cSDes1gn/ucl/src/logger.c

#include "logger.h"
#include "usart.h"
#include <stdarg.h>

// program log level (disable by default)
static enum log_level _level = LOG_DISABLE;

/**
 * @brief Get the string representation of log level enum
 *
 * @param level log level enum
 * @return char*
 */
static char *_get_level_str(enum log_level level) {
  switch (level) {
    case LOG_TRACE:
      return "TRACE";
    case LOG_INFO:
      return "INFO";
    case LOG_WARNING:
      return "WARN";
    case LOG_ERROR:
      return "ERROR";
    default:
      return "CRIT";
  }
}

/**
 * @brief Set the program log level
 *
 * @param level target logging level
 */
void logger_set_level(enum log_level level) { _level = level; }

/**
 * @brief Get the program log level
 *
 * @return enum Level
 */
enum log_level logger_get_level(void) { return _level; }

/**
 * @brief Perform log filtration and standard log construction parsing variable
 * arguments
 *
 * @param level log level enum
 * @param func macro expanded log containing function name
 * @param line macro expanded log line
 * @param fmt log string formatter
 * @param ... variable arguments for string formatter
 */
void logger_out(const enum log_level level, const char *func, const int line,
                const char *fmt, ...) {
  char buffer[1000];
  va_list args;
  // filter output by log level
  if (logger_get_level() > level) {
    return;
  }
  sprintf(buffer, "[%s]\t %s:%i ", _get_level_str(level), func, line);
  va_start(args, fmt);
  usart_println(buffer);
  vsprintf(buffer, fmt, args);
  va_end(args);
  usart_println(buffer);
  usart_println("\n\r");
}
